nguyen-v/epuck-artist/src/modules/mod_state.c

/**
 * @file    mod_state.c
 * @brief   Handles different states/modes and commands of the e-puck.
 */

// C standard header files

#include <stdio.h>
#include <stdlib.h>

// ChibiOS headers

#include "ch.h"
#include "hal.h"
#include "memory_protection.h"
#include "chprintf.h"
#include <usbcfg.h>

// Module headers

#include <mod_state.h>
#include <mod_draw.h>
#include <mod_communication.h>
#include <mod_data.h>
#include <mod_calibration.h>
#include <mod_img_processing.h>
#include <def_epuck_field.h>

/*===========================================================================*/
/* Module constants.                                                         */
/*===========================================================================*/

// List of possible commands sent from the computer

#define CMD_RESET          'R'
#define CMD_PAUSE          'P'
#define CMD_CONTINUE       'C'
#define CMD_SIGNAL_COLOR   'S'
#define CMD_CALIBRATE      'B'
#define CMD_GET_DATA       'G'
#define CMD_DRAW           'D'
#define CMD_IMAGE          'I'
#define CMD_HOME           'H'
#define CMD_VALIDATE       'V'


// Periods

#define CMD_PERIOD         100

/*===========================================================================*/
/* Module thread pointers.                                                   */
/*===========================================================================*/

static thread_t* ptr_process_cmd;

/*===========================================================================*/
/* Module local functions.                                                   */
/*===========================================================================*/


/**
 * @brief               Processes command and calls relevant module functions.
 *
 * @param[in]   cmd     Command. Possible commands listed in module constants.
 */
static void process_command(uint8_t cmd)
{
	switch (cmd) {
		case CMD_RESET:
			draw_stop_thd();
			cal_stop_thd();
			cal_stop_home_thd();
			draw_move(X_DEFAULT, Y_DEFAULT);
			draw_reset();
//			com_request_color(none);
			break;
		case CMD_PAUSE:
			draw_pause_thd();
			break;
		case CMD_CONTINUE:
			draw_resume_thd();
			break;
		case CMD_SIGNAL_COLOR:
			cal_signal_changed_colors();
			draw_signal_changed_colors();
			break;
		case CMD_CALIBRATE:
			if ((draw_get_state() || cal_get_home_state()) == false)
				cal_create_thd();
			break;
		case CMD_GET_DATA:
			com_receive_data((BaseSequentialStream *)&SD3);
			break;
		case CMD_DRAW:
			if ((cal_get_state() || cal_get_home_state()) == false)
				draw_create_thd();
			break;
		case CMD_IMAGE:
			if (draw_get_state() == false)
				capture_image();
			break;
		case CMD_HOME:
			if ((draw_get_state() || cal_get_state()) == false)
				cal_create_home_thd();
			break;
		case CMD_VALIDATE:
			cal_set_goal_distance();
			break;
	}
}

/*===========================================================================*/
/* Module threads.                                                           */
/*===========================================================================*/

/**
 * @brief                Thread for reading command from serial (SD3).
 *
 */
static THD_WORKING_AREA(wa_process_cmd, 1024);
static THD_FUNCTION(thd_process_cmd, arg)
{
	chRegSetThreadName(__FUNCTION__);
	(void)arg;

	while (1) {
		uint8_t cmd = com_receive_command((BaseSequentialStream *)&SD3);
		process_command(cmd);
		chThdSleepMilliseconds(CMD_PERIOD);
	}
}

/*===========================================================================*/
/* Module exported functions.                                                */
/*===========================================================================*/

void create_thd_process_cmd(void)
{
	ptr_process_cmd = chThdCreateStatic(wa_process_cmd, sizeof(wa_process_cmd),
	                                    NORMALPRIO+1, thd_process_cmd, NULL);
}
