nguyen-v/epuck-artist/src/main.h

#ifndef _MAIN_H_
#define _MAIN_H_

#ifdef __cplusplus
extern "C" {
#endif

#include "msgbus/messagebus.h"
#include "parameter/parameter.h"

/** Robot wide IPC bus. */
extern messagebus_t bus;

extern parameter_namespace_t parameter_root;

#ifdef __cplusplus
}
#endif



#endif
