nguyen-v/epuck-artist/src/modules/include/mod_communication.h

/**
 * @file    mod_communication.h
 * @brief   E-puck 2 communication to PC header.
 */

#ifndef _MOD_COMMUNICATION_H_
#define _MOD_COMMUNICATION_H_

/*===========================================================================*/
/* Module data structures and types.                                         */
/*===========================================================================*/

typedef enum message_type {
	MSG_COLOR,
	MSG_IMAGE_RGB,
	MSG_IMAGE_GRAYSCALE,
	MSG_IMAGE_GAUSS,
	MSG_IMAGE_SOBEL_MAG,
	MSG_IMAGE_LOCAL_THR,
	MSG_IMAGE_CANNY,
	MSG_IMAGE_PATH
} message_type;

/*===========================================================================*/
/* External declarations.                                                    */
/*===========================================================================*/

/**
 * @brief                Starts serial communication.
 * @note                 UART3 is connected to COM8 (Bluetooth).
 */
void com_serial_start(void);

/**
 * @brief                Returns true if e-puck is currently reading data.
 * @return               Bool indicating reading state of e-puck.
 */
bool data_ready(void);

/**
 * @brief                Reads a command from the computer.
 * @param[in]   in       Pointer to a @p BaseSequentialStream or derived class
 * @return               An utf-8 encoded command
 */
uint8_t com_receive_command(BaseSequentialStream* in);

/**
 * @brief                Reads length data (uint8) from the computer.
 * @param[in]   in       Pointer to a @p BaseSequentialStream or derived class
 * @returnm              Length in mm
 */
uint8_t com_receive_length(BaseSequentialStream* in);

/**
 * @brief                Reads position and color data from the computer and
 *                       and fills corresponding buffers.
 * @param[in]   in       Pointer to a @p BaseSequentialStream or derived class
 * @param[out]  pos      Pointer to position buffer @p cartesian_coord
 * @return               Length of the position buffer.
 */
uint16_t com_receive_data(BaseSequentialStream* in);

/**
 * @brief                Sends data to the computer (uint8_t)
 * @param[in]   out      Pointer to a @p BaseSequentialStream or derived class
 * @param[in]   data     Pointer to buffer to be sent.
 * @param[in]   size     Size in bytes of data to be sent.
 * @param[in]   msg_type Type of message defined in enum message_type.
 * @return               none
 */
void com_send_data(BaseSequentialStream* out, uint8_t* data, uint16_t size,
                    message_type msg_type);

/**
 * @brief                Sends a color change request to the computer
 * @param[in]   col      Color defined in enum Colors
 * @return               none
 * @note                 The computer then sends this command via Bluetooth
 *                       to the arduino module.
 */
void com_request_color(uint8_t col);

#endif /* _MOD_COMMUNICATION_H_ */
