nguyen-v/epuck-artist/src/modules/include/mod_calibration.h

/**
 * @file    mod_calibration.h
 * @brief   External declarations of calibration module.
 */

#ifndef _MOD_CALIBRATION_H_
#define _MOD_CALIBRATION_H_

/*===========================================================================*/
/* Exported constants                                                        */
/*===========================================================================*/

#define DEFAULT_HEIGHT_CM     100 // cm

/*===========================================================================*/
/* External declarations.                                                    */
/*===========================================================================*/

/**
 * @brief                        Creates calibration thread
 * @return                       none
 */
void cal_create_thd(void);

/**
 * @brief                        Stops calibration thread
 * @return                       True calibration distance in steps
 */
uint16_t cal_stop_thd(void);

/**
 * @brief                        Sets goal calibration distance
 * @return                       none
 */
void cal_set_goal_distance(void);

/**
 * @brief                        Returns current calibration state
 * @return                       True if currently calibrating, false otherwise
 */
bool cal_get_state(void);

/**
 * @brief                        Signals that color has changed
 * @return                       none
 */
void cal_signal_changed_colors(void);

/**
 * @brief                        Creates thread to set top center of canvas
 * @return                       none
 */
void cal_create_home_thd(void);

/**
 * @brief                        Stops set home thread
 * @return                       none
 */
void cal_stop_home_thd(void);

/**
 * @brief                        Returns current set home thread state
 * @return                       True if currently setting home, false otherwise
 */
bool cal_get_home_state(void);

#endif /* _MOD_CALIBRATION_H_ */
